DC801/DC26PartyBadge/Hardware/images/board_shape.png

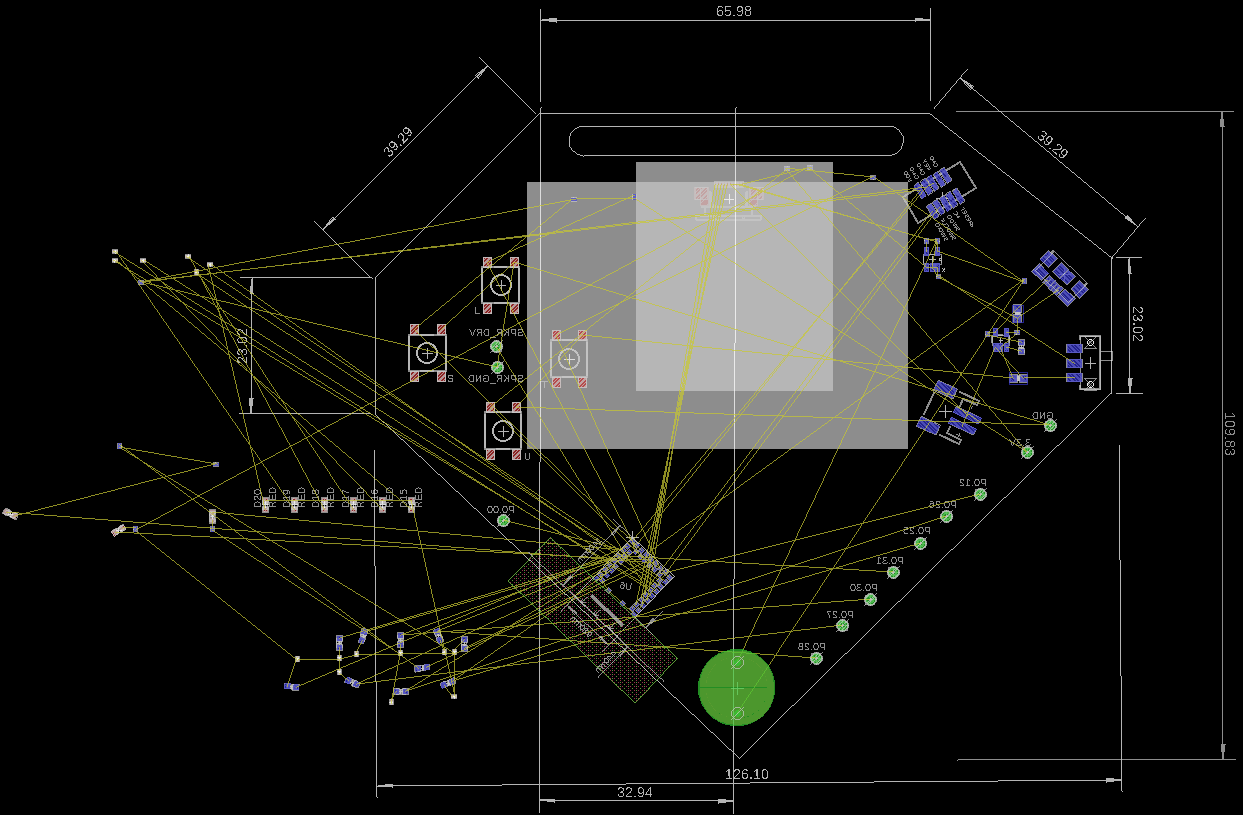
Hardware/images/board_shape.png
