DC801/DC26PartyBadge/Hardware/images/DC26_Board.png

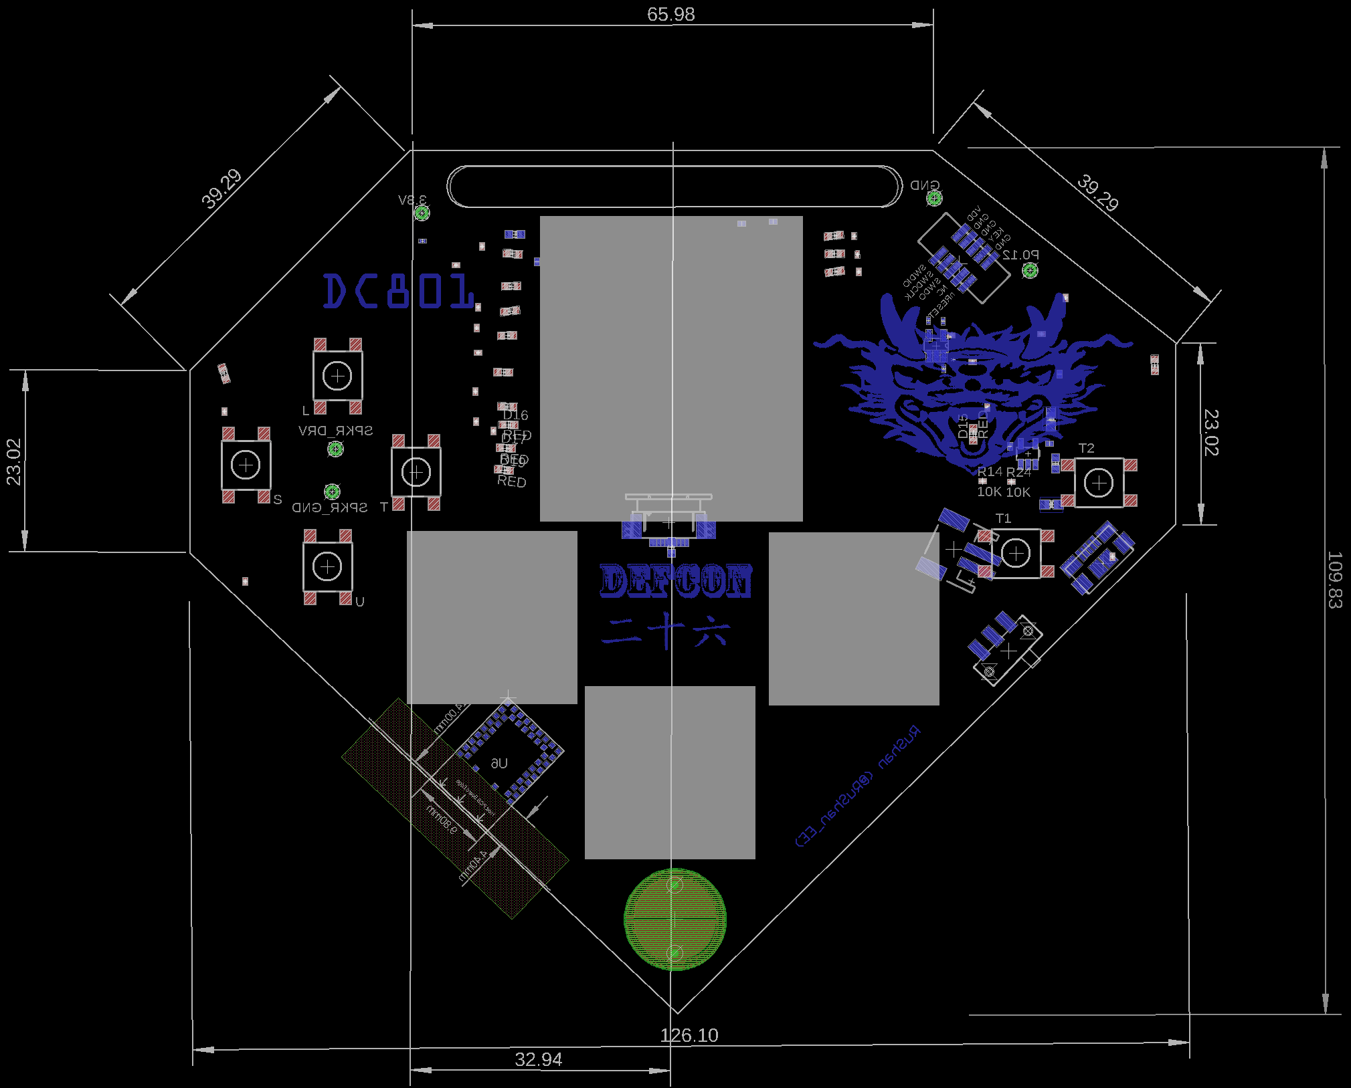
Hardware/images/DC26_Board.png
