DC801/DC26PartyBadge/Hardware/images/defcon.png

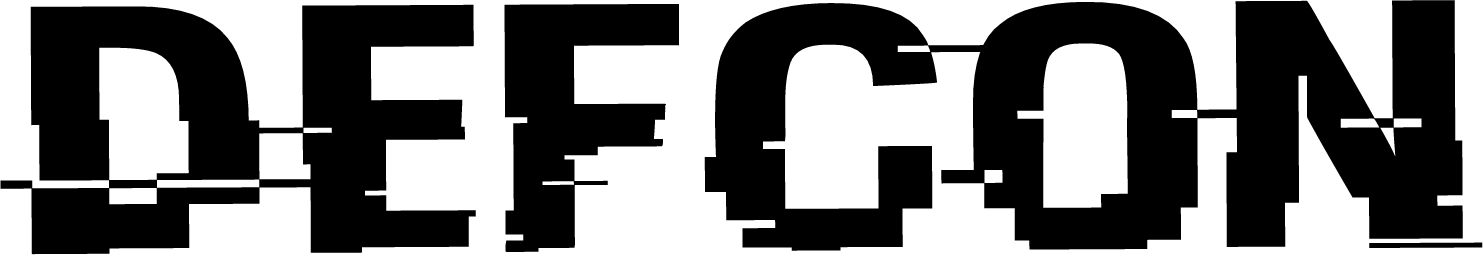
Hardware/images/defcon.png
