DC801/DC26PartyBadge/Hardware/images/dragon-joke.png

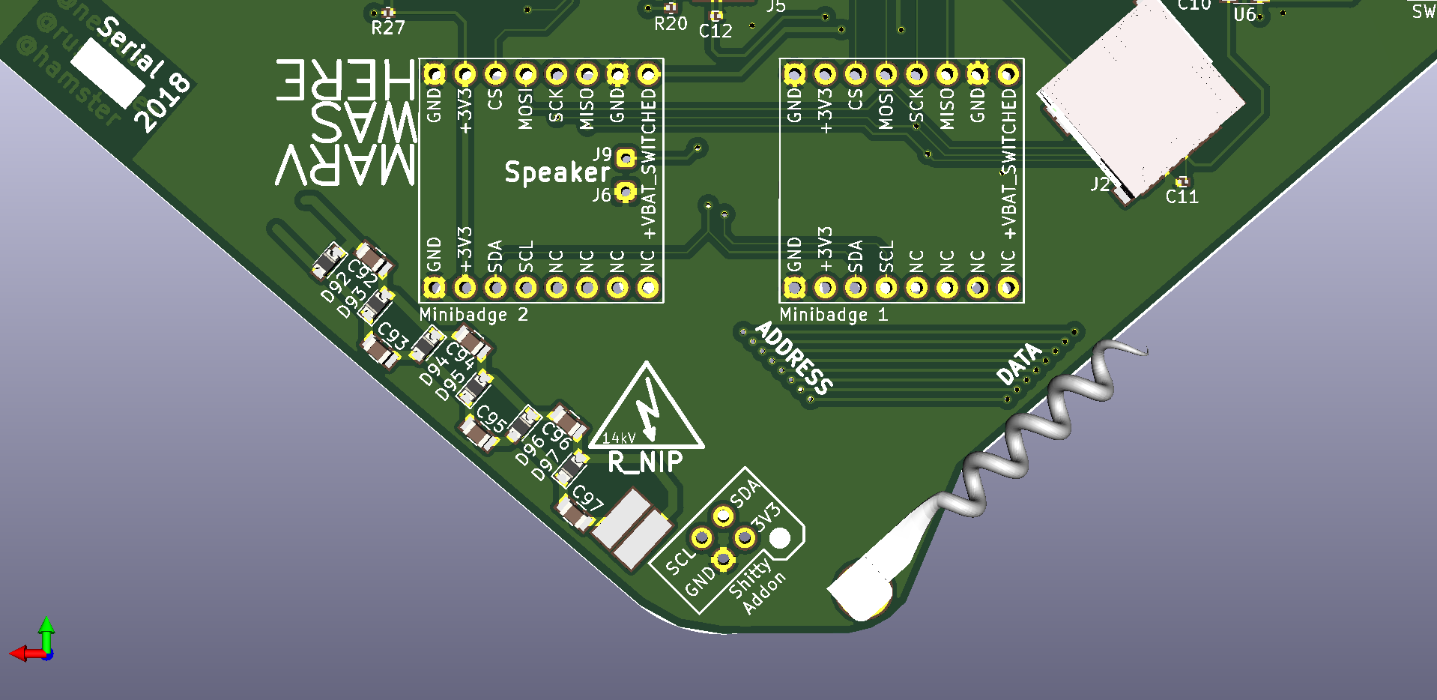
Hardware/images/dragon-joke.png
