DC801/DC26PartyBadge/Hardware/images/Dragon-ProtoFinal-Back.png

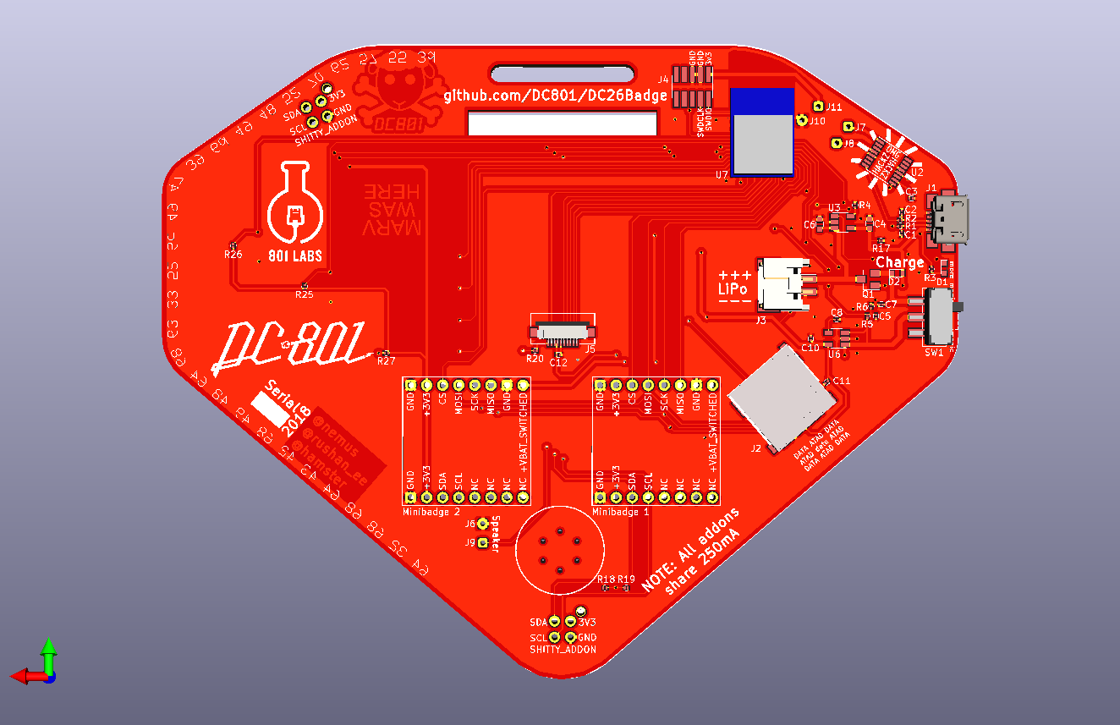
Hardware/images/Dragon-ProtoFinal-Back.png
