DC801/DC26PartyBadge/Hardware/images/DragonBoardBack1.png

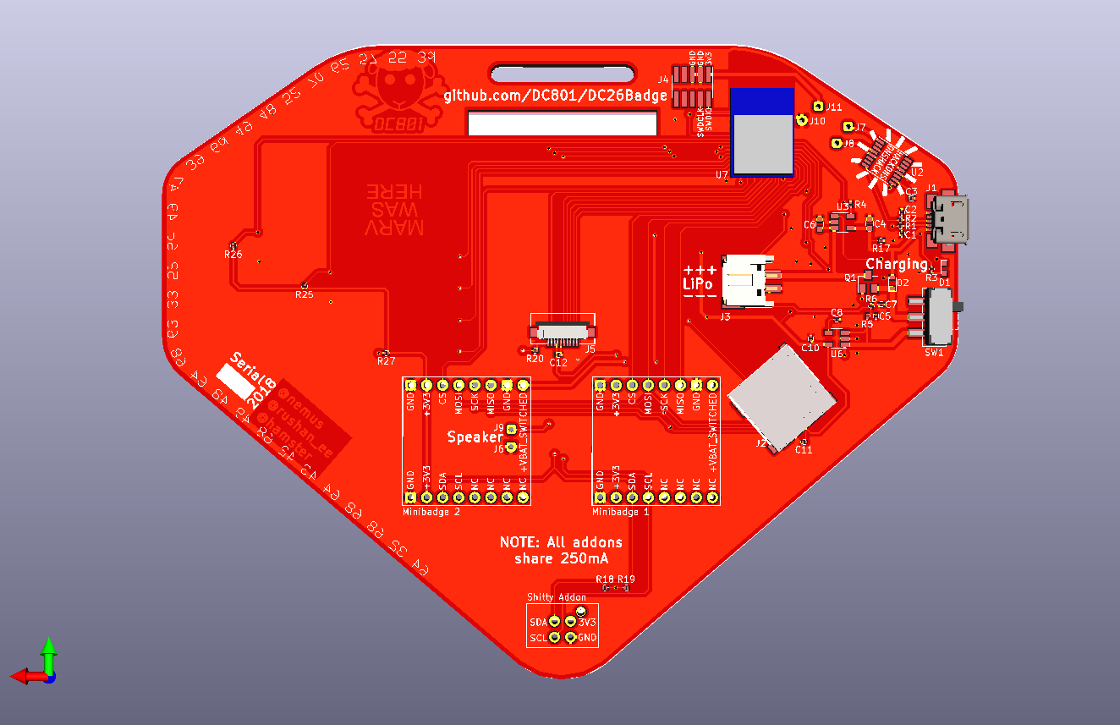
Hardware/images/DragonBoardBack1.png
