DC801/DC26PartyBadge/Hardware/images/DragonBoardFront-Final.png

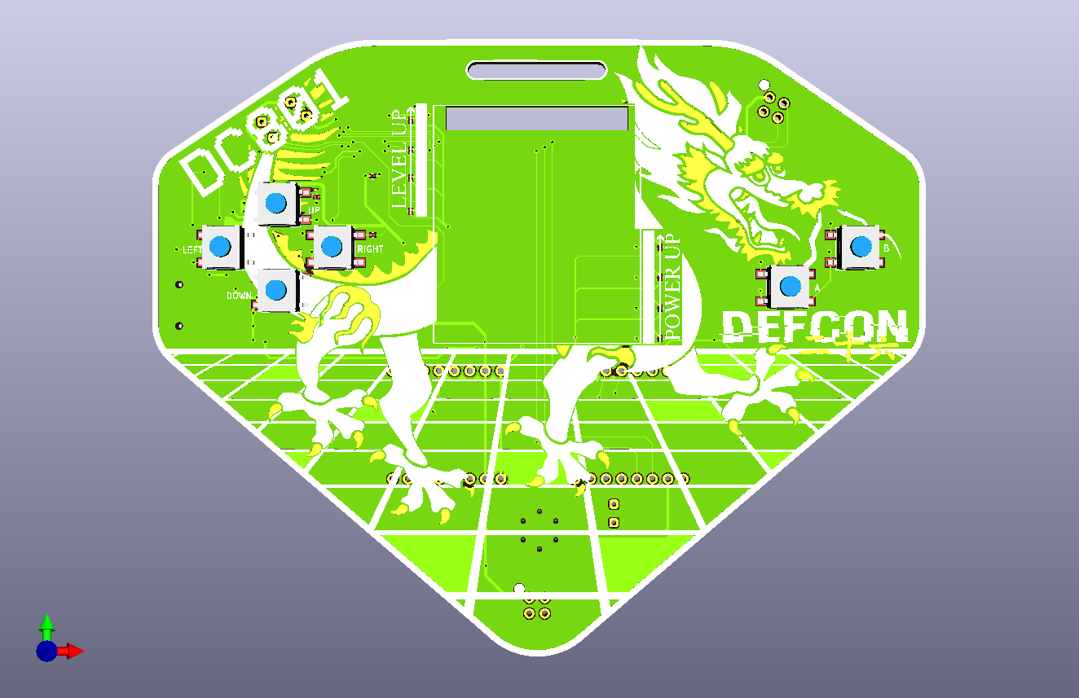
Hardware/images/DragonBoardFront-Final.png
