DC801/DC26PartyBadge/Hardware/images/DragonCopper.png

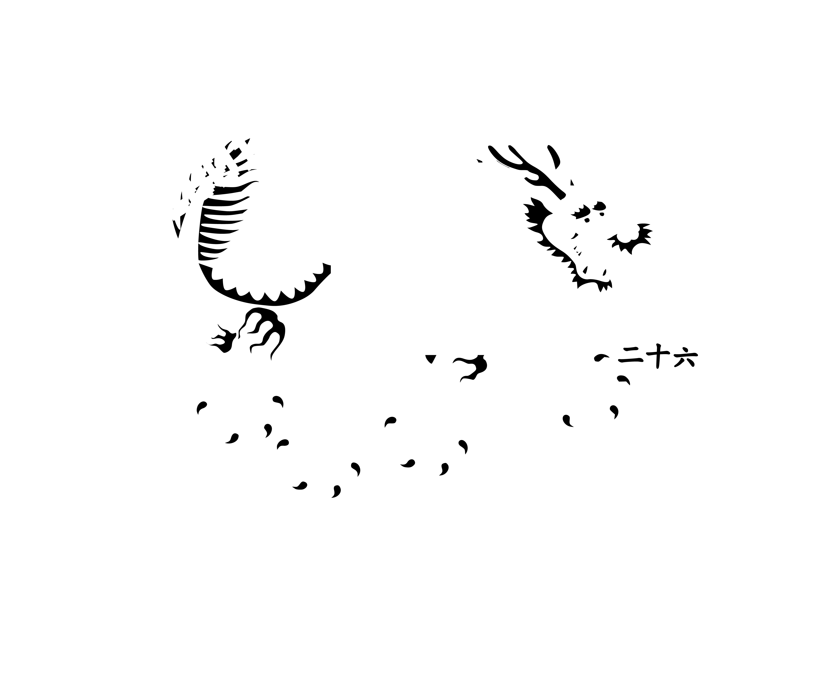
Hardware/images/DragonCopper.png
