DC801/DC26PartyBadge/Hardware/images/DragonExport.png

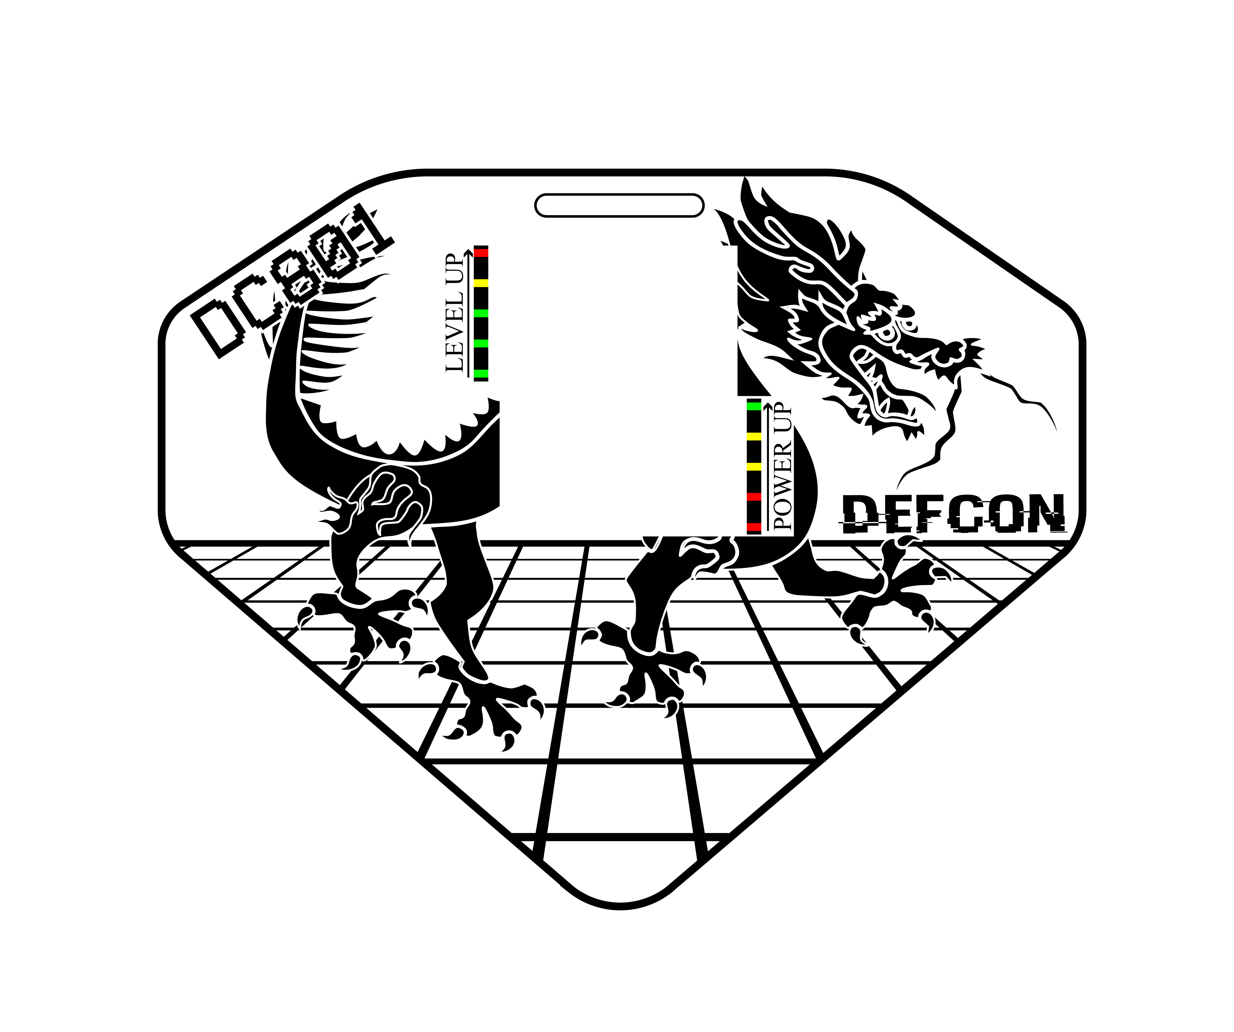
Hardware/images/DragonExport.png
