DC801/DC26PartyBadge/Hardware/images/DragonMockupBack1.png

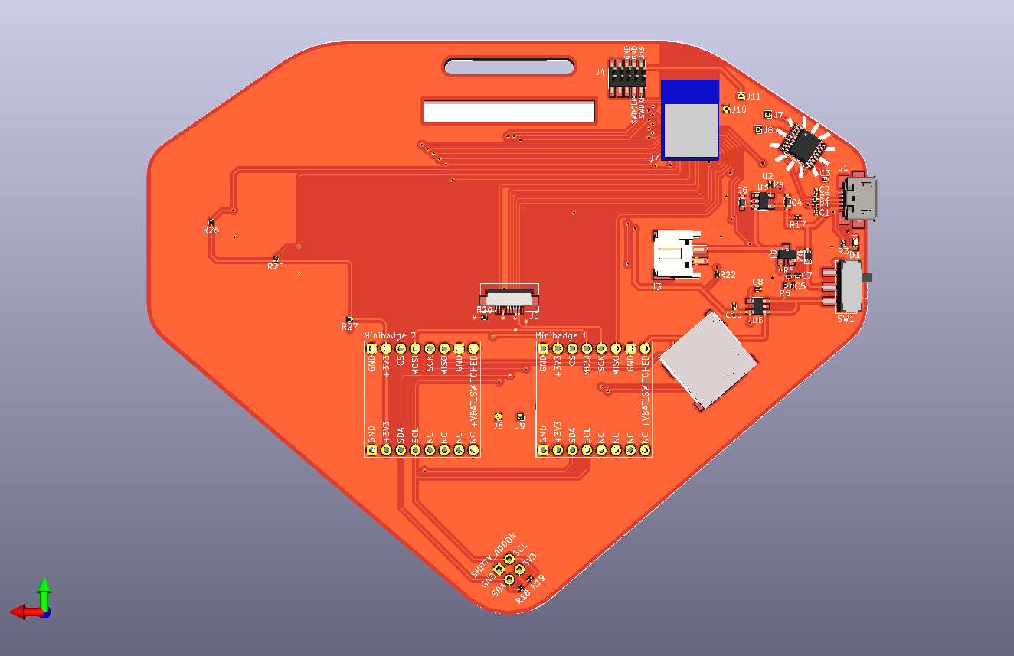
Hardware/images/DragonMockupBack1.png
