DC801/DC26PartyBadge/Hardware/images/DragonOutline.png

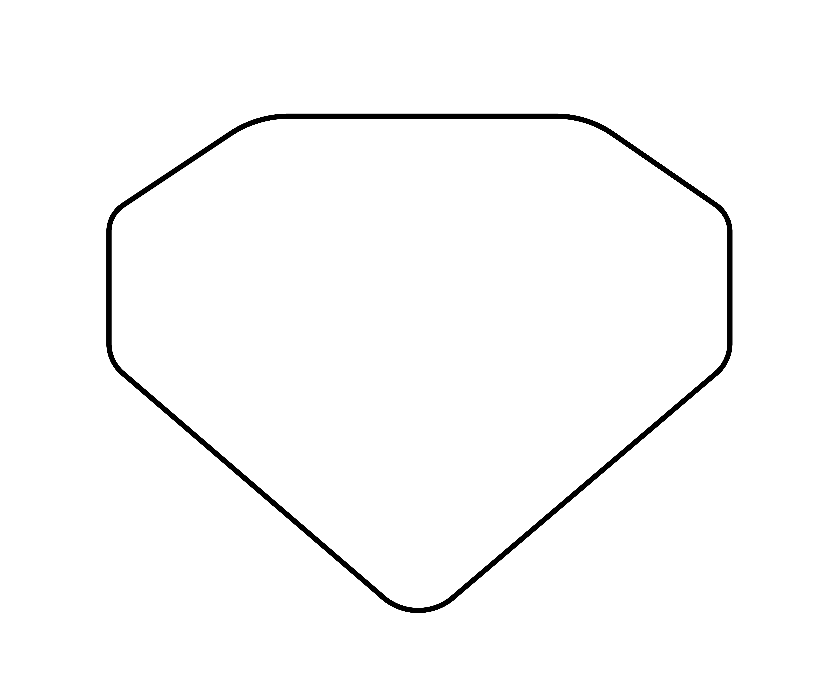
Hardware/images/DragonOutline.png
