DC801/DC26PartyBadge/Hardware/images/DragonText.png

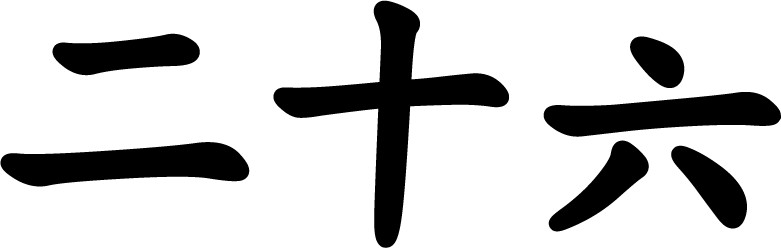
Hardware/images/DragonText.png
