DC801/DC26PartyBadge/Hardware/images/FTDI Starburst.png

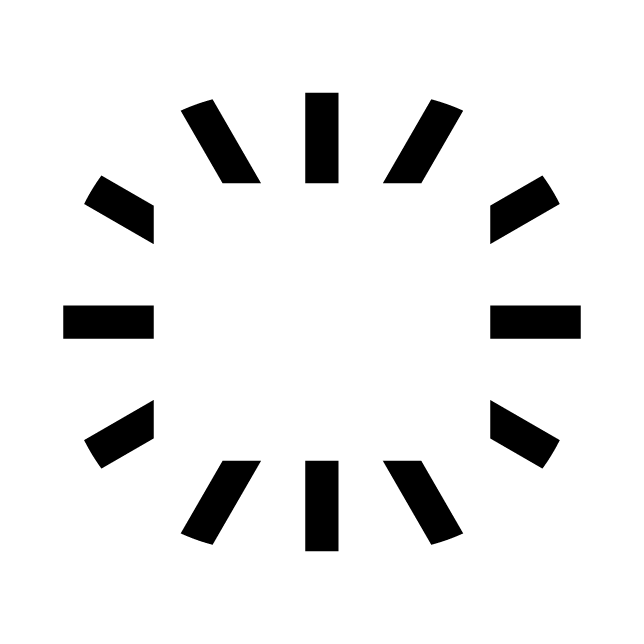
Hardware/images/FTDI Starburst.png
