DC801/DC26PartyBadge/Hardware/images/marv_was_here.png

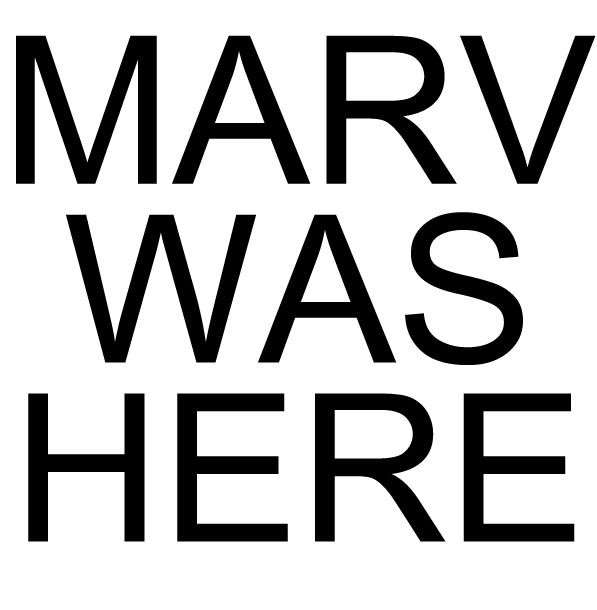
Hardware/images/marv_was_here.png
