DC801/DC26PartyBadge/Hardware/images/Schematic 1.0pre.png

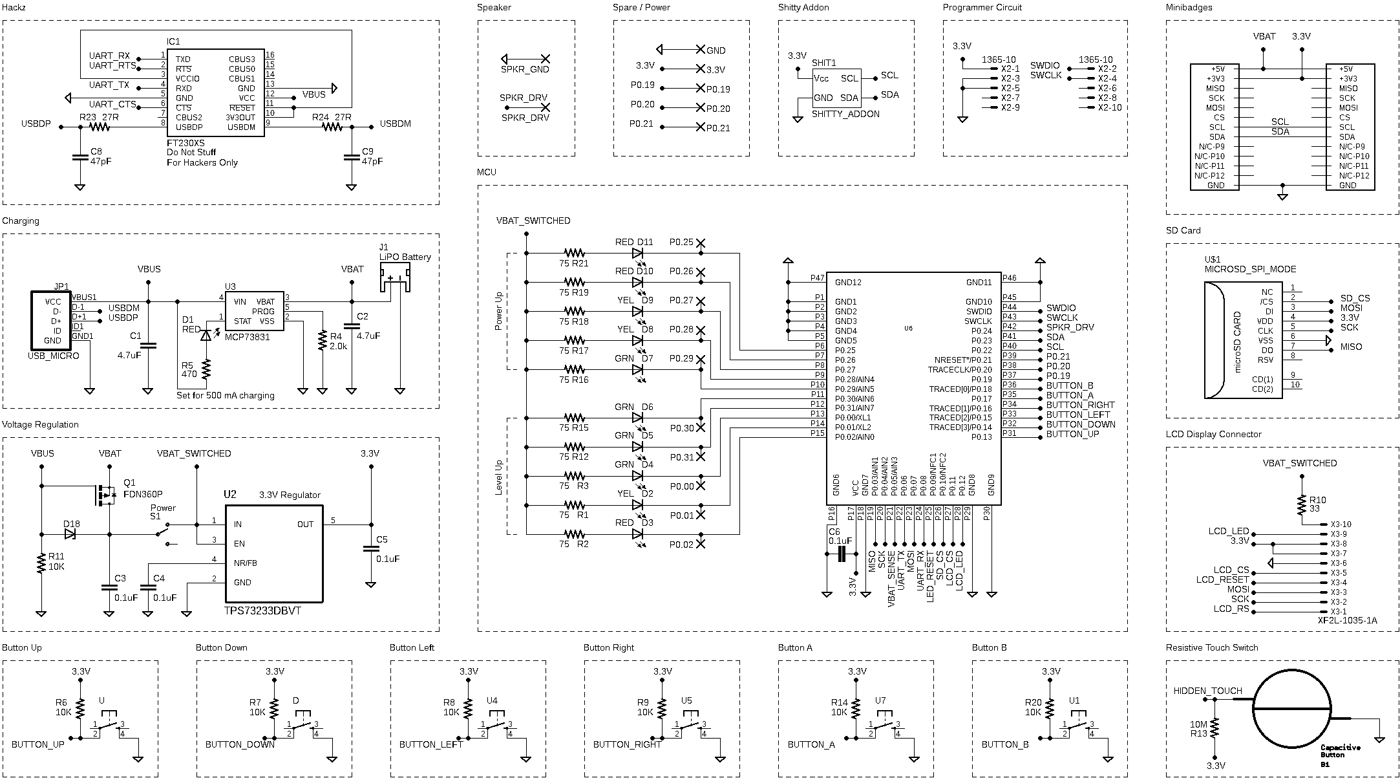
Hardware/images/Schematic 1.0pre.png
