DC801/DC26PartyBadge/Hardware/images/Sheep Head.png

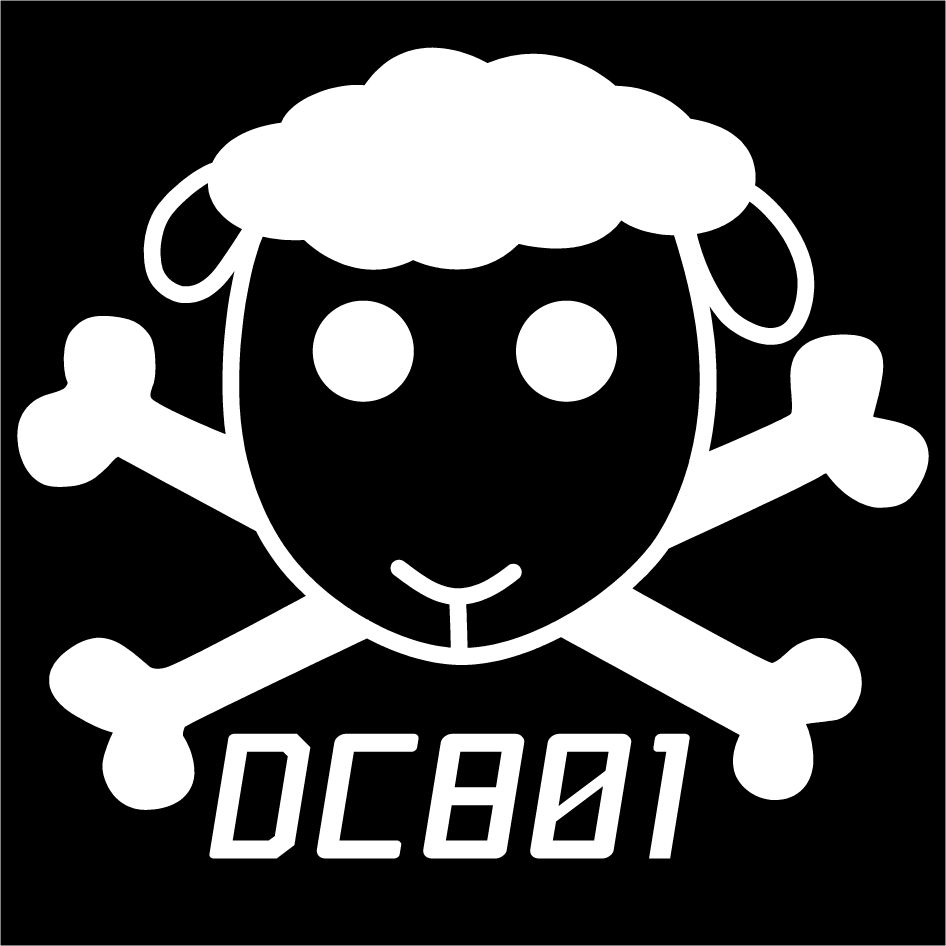
Hardware/images/Sheep Head.png
