DC801/DC26PartyBadge/Hardware/images/shitty.png

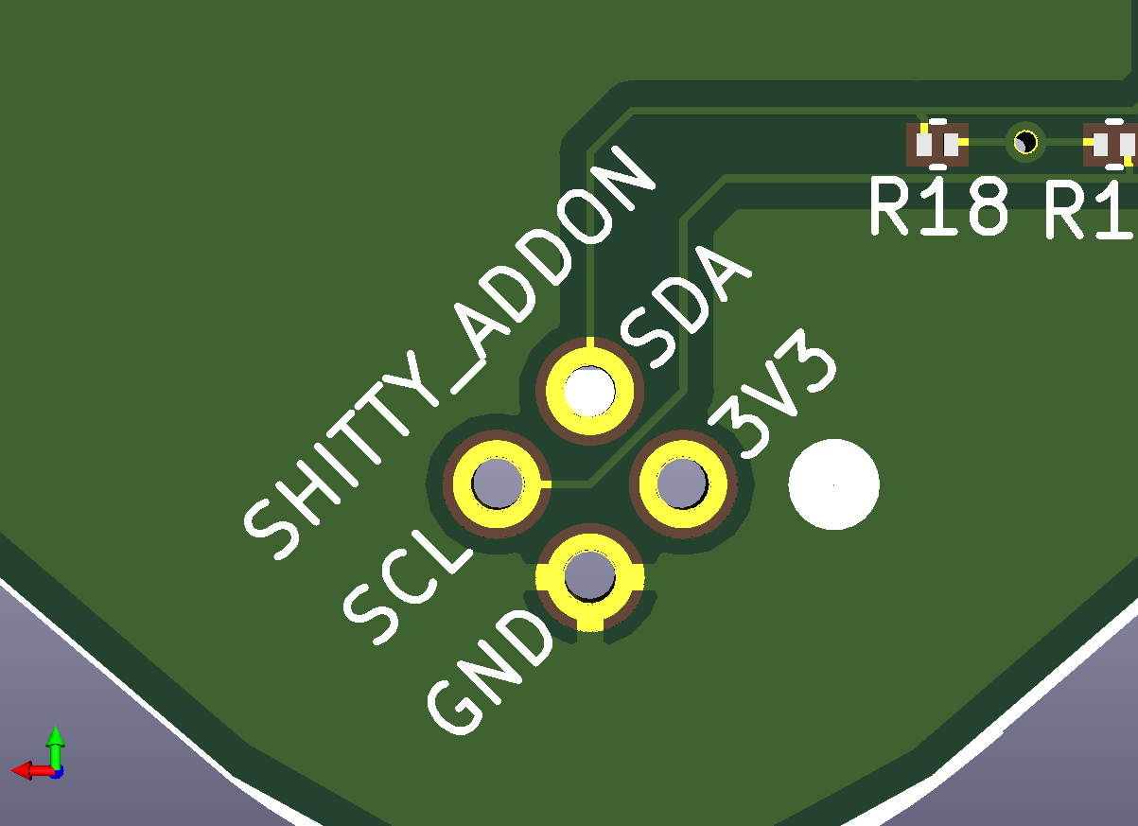
Hardware/images/shitty.png
