DC801/DC26PartyBadge/Hardware/images/DragonTest2.png

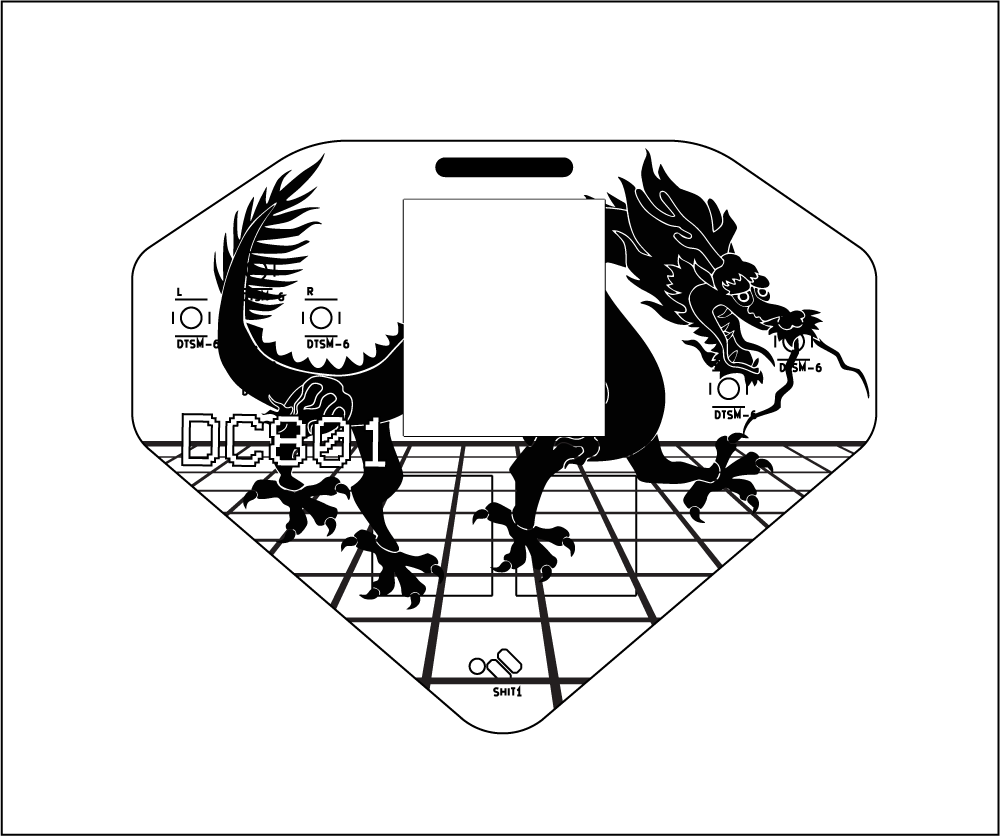
Hardware/images/DragonTest2.png
