DC801/DC26PartyBadge/Hardware/images/DragonTest4-Blue.png

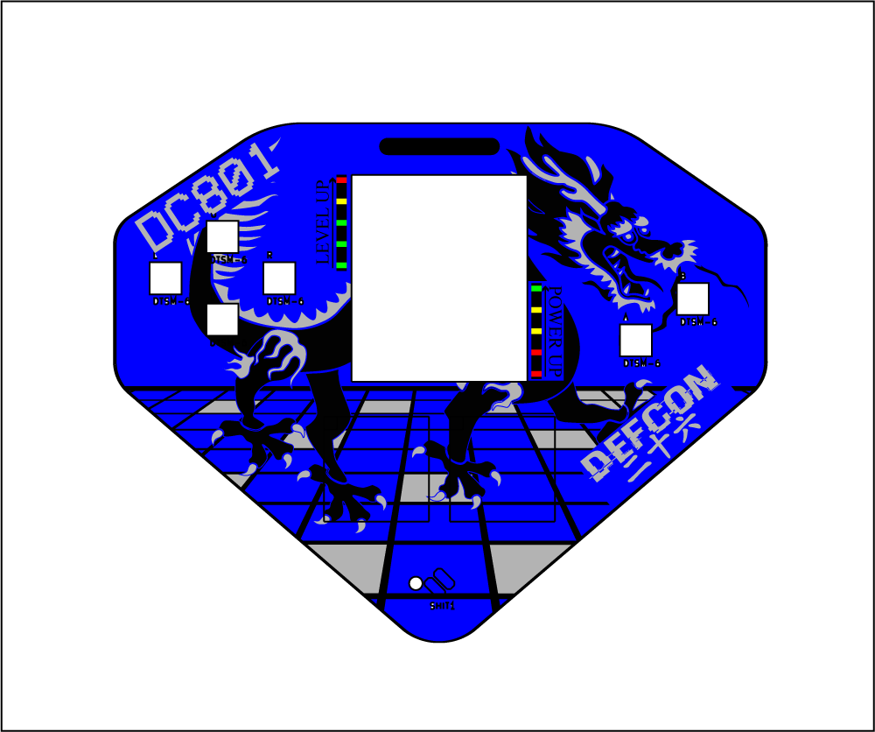
Hardware/images/DragonTest4-Blue.png
