DC801/DC26PartyBadge/Hardware/images/DragonTest.png

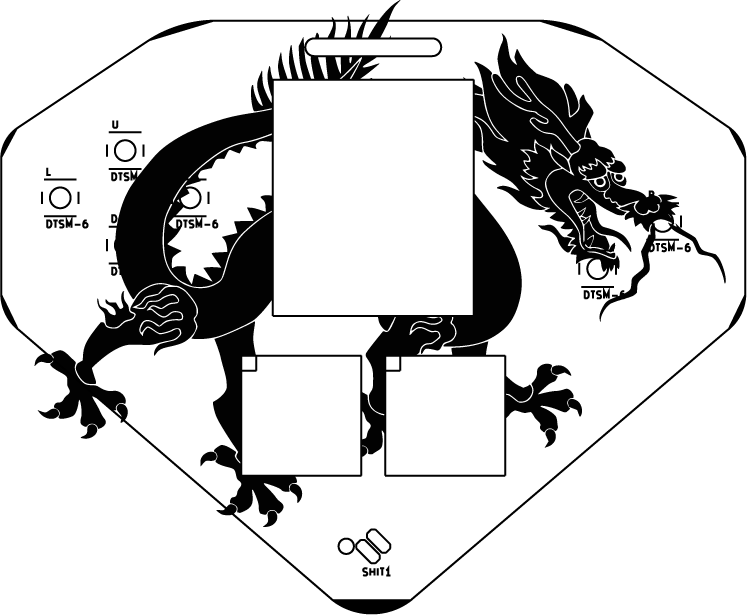
Hardware/images/DragonTest.png
