DC801/DC26PartyBadge/Software/modules/ble.h

/*
 * @file ble.h
 *
 * @date Jul 19, 2017
 * @author hamster
 *
 */

#ifndef BLE_H_
#define BLE_H_

#include <common.h>

#define DATA_SAVE_LEN 16

typedef struct{
	uint16_t appearance;
	uint16_t manu;
	uint8_t manu_data[DATA_SAVE_LEN];
	char *short_name;
	uint8_t short_name_len;
	char *long_name;
	uint8_t long_name_len;
} ADVERTISEMENT;

typedef enum {
    badgeYear_25    = 0x19DC,
    badgeYear_26    = 0x26DC,
    NUM_BADGE_YEARS
} BADGE_YEAR;

typedef enum {
    badge_none,
    badge_andnxor,
    badge_cpv,
    badge_darknet,
    badge_dc801,
    badge_dczia,
    badge_FoB,
    badge_diana,
    badge_dc503,
    badge_dcfurs,
    badge_blinky,
    badge_phase4_monkey,
    badge_phase4_ham,
    badge_queercon,
    badge_shotbot,
    badge_pirates,
    NUM_BADGE_GROUPS
} BADGE_GROUP;

#define FIRST_BADGE_GROUP   badge_andnxor
#define LAST_BADGE_GROUP    badge_pirates

typedef struct {
    BADGE_YEAR year;
    BADGE_GROUP group;
    uint16_t appearance;
    uint8_t data[DATA_SAVE_LEN];
    uint8_t name[DATA_SAVE_LEN + 1];
    uint8_t mac[6];
    int8_t rssi;
} BADGE_ADV;

typedef struct {
	BADGE_GROUP group;
	uint16_t appearance;
	char *name;
	char *icon;
	char *contact;
} BADGE_INFO;

extern const BADGE_INFO badgeInfo[NUM_BADGE_GROUPS - 1];

void ble_adv_init(void);
void ble_adv_start(void);
void ble_stack_init(void);
void gap_params_init(void);
void scan_start(void);

void advertising_setUser(char *user);
void advertising_setClan(uint8_t clan);
void advertising_setScore(uint32_t score);
void advertising_setGodCommand(GODMODE_COMMAND command, uint32_t data);

bool parseAdvertisementData(uint8_t *data, uint8_t len, ADVERTISEMENT *adv);


uint8_t getBadges(BADGE_ADV *badges);
bool getBadge(uint8_t index, BADGE_ADV *badge);
uint8_t getBadgeNum(void);
char* getBadgeGroupName(BADGE_GROUP group);
char* getBadgeIconFile(BADGE_GROUP group);
char* getBadgeContact(BADGE_GROUP group);
uint16_t getBadgeAppearance(BADGE_GROUP group);
BADGE_GROUP getBadgeGroupFromAppearance(uint16_t appearance);

bool checkForRabies(BADGE_ADV badge);
void handleGodMode(BADGE_ADV badge, int *modifier);


#define APP_COMPANY_IDENTIFIER_DC801    0x0801
#define APP_APPEARANCE_TYPE_DC26        0x26DC

#define BLOCK_TYPE_APPEARANCE	0x19
#define BLOCK_TYPE_MANU_INFO	0xFF
#define BLOCK_TYPE_LONG_NAME	0x09
#define BLOCK_TYPE_SHORT_NAME	0x08

#define APP_BLE_CONN_CFG_TAG 			1
#define APP_BLE_OBSERVER_PRIO           3

#define DEVICE_NAME                     "DC801   "                 				/**< Name of device. Will be included in the advertising data. */
#define NON_CONNECTABLE_ADV_INTERVAL    MSEC_TO_UNITS(500, UNIT_0_625_MS) 		/**< The advertising interval for non-connectable advertisement (100 ms).
																					This value can vary between 100ms to 10.24s). */

#define SCAN_INTERVAL                   MSEC_TO_UNITS(100, UNIT_0_625_MS)    	/**< Determines scan interval in units of 0.625 millisecond. */
#define SCAN_WINDOW                     MSEC_TO_UNITS(50, UNIT_0_625_MS)    	/**< Determines scan window in units of 0.625 millisecond. */
#define SCAN_TIMEOUT                    0

#define MIN_CONN_INTERVAL               MSEC_TO_UNITS(100, UNIT_1_25_MS)        /**< Minimum acceptable connection interval (0.1 seconds). */
#define MAX_CONN_INTERVAL               MSEC_TO_UNITS(200, UNIT_1_25_MS)        /**< Maximum acceptable connection interval (0.2 second). */
#define SLAVE_LATENCY                   0                                       /**< Slave latency. */
#define CONN_SUP_TIMEOUT                MSEC_TO_UNITS(4000, UNIT_10_MS)         /**< Connection supervisory timeout (4 seconds). */

#define DEFCON_BADGE_SCAN_INTERVAL		APP_TIMER_TICKS(15000)

#define NUM_BADGES_TO_STORE             16

#define FURRY_HAS_RABIES                0x35
#define COMMAND_SEND_EMOTE              0xb2

#endif /* BLE_H_ */
