DC801/DC26PartyBadge/Software/common.h

/*
 * @file system.h
 *
 * @date May 24, 2017
 * @author hamster
 *
 * Common header file included by all files in the project
 * This will pull in all the other header files so our includes are neater
 *
 */

#ifndef SYSTEM_H_
#define SYSTEM_H_

// System headers
#include <ctype.h>
#include <math.h>
#include <stdbool.h>
#include <stdlib.h>
#include <string.h>
#include <sys/time.h>

#include "config/app/sdk_config.h"
#include "config/custom_board.h"

// Nordic headers 
#include "nordic_common.h"
#include "nrf.h"
#include "app_error.h"
#include "ble.h"
#include "ble_err.h"
#include "ble_hci.h"
#include "ble_srv_common.h"
#include "ble_advdata.h"
#include "ble_conn_params.h"
#include "bsp.h"
#include "nrf_sdh.h"
#include "nrf_sdh_ble.h"
#include "boards.h"
#include "app_timer.h"
#include "app_button.h"
#include "ble_lbs.h"
#include "nrf_ble_gatt.h"
#include "nrf_ble_qwr.h"
#include "nrf_pwr_mgmt.h"
#include "nrf_delay.h"
#include "nrf_drv_clock.h"
#include "nrf52.h"
#include "nrf52832_peripherals.h"
#include "nrf_spim.h"
#include "nrf_drv_spi.h"
#include "ff.h"
#include "nrf_block_dev_sdc.h"
#include "nrf_block_dev.h"
#include "diskio.h"
#include "diskio_blkdev.h"
#include "legacy/nrf_drv_rng.h"
#include "nrf_drv_saadc.h"
#include "nrf_saadc.h"
#include "nrf_drv_ppi.h"
#include "nrf_drv_timer.h"
#include "app_uart.h"

#include "nrf_log.h"
#include "nrf_log_ctrl.h"
#include "nrf_log_default_backends.h"

#define printf NRF_LOG_RAW_INFO

typedef enum{
    gm_command_none,
    gm_command_addscoremodifier,
    gm_command_addscore,
    gm_command_party,
    gm_command_sheep,
    gm_command_beep
} GODMODE_COMMAND;

// Includes for our app
#include "utility.h"
#include "main.h"
#include "menu.h"
#include "user.h"
#include "nearby.h"
#include "extras.h"
#include "modules/ble.h"
#include "godmode.h"
#include "modules/drv_st7735.h"
#include "modules/gfx.h"
#include "modules/sd.h"
#include "modules/adc.h"
#include "modules/uart.h"
#include "adafruit/gfxfont.h"
#include "games/Space_Invaders.h"
#include "games/Snake.h"
#include "games/PipsTheET.h"
#include "games/Tic-Tac-Toe.h"
#include "games/Wargames.h"


#endif /* SYSTEM_H_ */
